transistorfet/z280/software/src/monitor/monitor.c

#include <stdio.h>
#include <stdint.h>
#include <string.h>
#include <stdlib.h>

#include "uart.h"


#define ROM_ADDR	0x000000
#define ROM_SIZE	0x1800

#define RAM_ADDR	0x2000
#define RAM_SIZE	1024

void delay(int count)
{
	while (--count > 0) { __asm__(""); }
}

int readline(char *buffer, short max)
{
	short i = 0;

	while (i < max) {
		buffer[i] = getchar();
		switch (buffer[i]) {
			case 0x08: {
				if (i >= 1) {
					putchar(0x08);
					putchar(' ');
					putchar(0x08);
					i--;
				}
				break;
			}
			case '\n': {
				putchar(buffer[i]);
				buffer[i] = '\0';
				return i;
			}
			default: {
				putchar(buffer[i++]);
				break;
			}
		}
	}
	return i;
}

int parseline(char *input, char **vargs)
{
	short j = 0;

	while (*input == ' ')
		input++;

	vargs[j++] = input;
	while (*input != '\0' && *input != '\n' && *input != '\r') {
		if (*input == ' ') {
			*input = '\0';
			input++;
			while (*input == ' ')
				input++;
			vargs[j++] = input;
		}
		else
 			input++;
	}

	*input = '\0';
	if (*vargs[j - 1] == '\0')
		j -= 1;
	vargs[j] = NULL;

	return j;
}

char hexchar(uint8_t byte)
{
    if (byte < 10)
	return byte + 0x30;
    else
	return byte + 0x37;
}

void dump(const uint8_t *addr, short len)
{
	char buffer[4];

	buffer[2] = ' ';
	buffer[3] = '\0';
	while (len > 0) {
		printf("%x: ", addr);
		for (short i = 0; i < 16 && len > 0; i++, len--) {
			buffer[0] = hexchar((addr[i] >> 4) & 0xF);
			buffer[1] = hexchar(addr[i] & 0x0F);
			fputs(buffer, stdout);
		}
		putchar('\n');
		addr += 16;
	}
	putchar('\n');
}

void command_dump(int argc, char **args)
{
	if (argc <= 1)
		fputs("You need an address\n", stdout);
	else {
		short length = 0x40;

		if (argc >= 3)
			length = strtol(args[2], NULL, 16);
		dump((const uint16_t *) strtol(args[1], NULL, 16), length);
	}
}

void command_poke(int argc, char **args)
{
	if (argc <= 2)
		fputs("You need an address and byte to poke\n", stdout);
	else {
		uint8_t *address = (uint8_t *) strtol(args[1], NULL, 16);
		uint8_t data = (uint8_t) strtol(args[2], NULL, 16);
		*(address) = data;
	}

}

/*
#define SECTOR_SIZE	0x020000

void erase_flash(uint32_t sector)
{
	printf("Erasing flash sector %d", sector);
	*((volatile uint16_t *) (0x555 << 1)) = 0xAAAA;
	putchar('.');
	*((volatile uint16_t *) (0x2AA << 1)) = 0x5555;
	putchar('.');
	*((volatile uint16_t *) (0x555 << 1)) = 0x8080;
	putchar('.');
	*((volatile uint16_t *) (0x555 << 1)) = 0xAAAA;
	putchar('.');
	*((volatile uint16_t *) (0x2AA << 1)) = 0x5555;
	putchar('.');
	*((volatile uint16_t *) sector) = 0x3030;
	putchar('.');
}

void command_eraserom(int argc, char **args)
{
	uint16_t data;
	uint16_t *dest = (uint16_t *) ROM_ADDR;
	uint32_t sector = 0;

	if (argc >= 2) {
		sector = strtol(args[1], NULL, 16);
		if ((sector & (SECTOR_SIZE - 1)) || (sector >= RAM_ADDR)) {
			printf("Invalid sector address to erase (%x)\n", sector);
			return;
		}
		dest = (uint16_t *) sector;
	}

	erase_flash(sector);
	delay(300000);
	data = dest[0];

	fputs("\nVerifying erase\n\n", stdout);
	for (int i = 0; i < ROM_SIZE; i++) {
		data = dest[i];
		if (data != 0xFFFF) {
			printf("Flash not erased at %x (%x)\n", dest + i, data);
			return;
		}
	}

	fputs("Rom erased! Make sure to writerom before resetting\n\n", stdout);
}

void program_flash_data(uint16_t *addr, uint16_t data)
{
	*((volatile uint16_t *) (0x555 << 1)) = 0xAAAA;
	*((volatile uint16_t *) (0x2AA << 1)) = 0x5555;
	*((volatile uint16_t *) (0x555 << 1)) = 0xA0A0;
	*((volatile uint16_t *) addr) = data;
}

void command_writerom(int argc, char **args)
{
	uint16_t data;
	uint16_t errors = 0;

	uint16_t *dest = (uint16_t *) ROM_ADDR;
	uint16_t *source = (uint16_t *) RAM_ADDR;

	if (argc >= 2)
		dest = (uint16_t *) strtol(args[1], NULL, 16);

	for (int i = 0; i < ROM_SIZE; i++) {
		data = dest[i];
		if (data != 0xFFFF) {
			printf("Flash not erased at %x (%x)\n", dest + i, data);
			return;
		}
	}

	for (int i = 0; i < ROM_SIZE; i++) {
		program_flash_data(&dest[i], source[i]);
		delay(200);
		printf("%x ", dest[i]);
	}

	fputs("\nWrite complete\n", stdout);
}

void command_verifyrom(int argc, char **args)
{
	uint16_t data;
	uint16_t errors = 0;

	uint16_t *source = (uint16_t *) RAM_ADDR;
	uint16_t *dest = (uint16_t *) ROM_ADDR;

	if (argc >= 2)
		dest = (uint16_t *) strtol(args[1], NULL, 16);

	for (int i = 0; i < ROM_SIZE; i++) {
		if (dest[i] != source[i]) {
			printf("@%x expected %x but found %x\n", &dest[i], source[i], dest[i]);
			if (++errors > 100) {
				fputs("Bailing out\n", stdout);
				break;
			}
		}
	}

	fputs("\nVerification complete\n", stdout);
}
*/


uint8_t fetch_byte()
{
	char buffer[2];

	for (char i = 0; i < 2; i++) {
		buffer[i] = getchar();
		buffer[i] = buffer[i] <= '9' ? buffer[i] - 0x30 : buffer[i] - 0x37;
	}

	return (buffer[0] << 4) | buffer[1];
}

uint16_t fetch_word()
{
	char buffer[4];

	for (char i = 0; i < 4; i++) {
		buffer[i] = getchar();
		buffer[i] = buffer[i] <= '9' ? buffer[i] - 0x30 : buffer[i] - 0x37;
	}

	return (buffer[0] << 12) | (buffer[1] << 8) | (buffer[2] << 4) | buffer[3];
}

void command_load(int argc, char **args)
{
	int i;
	uint32_t size;
	uint16_t data;
	uint8_t *mem = (uint8_t *) RAM_ADDR;

	size = fetch_word();
	//printf("Expecting %x\n", size);

	if (argc >= 2)
		mem = (uint8_t *) strtol(args[1], NULL, 16);

	for (i = 0; i < size; i++) {
		data = fetch_byte();
		//printf("%x ", data);
		mem[i] = data;
	}

	fputs("Load complete\n", stdout);
}



void command_boot(int argc, char **args)
{
	void (*entry)() = (void (*)()) RAM_ADDR;

	if (argc >= 2)
		entry = (void (*)()) strtol(args[1], NULL, 16);
	//((void (*)()) entry)();
}

void command_serialtest(int argc, char **args)
{
	while (1) {
		int ch = getchar();
		if (ch == 0x1B)
			break;
		putchar(hexchar(ch >> 4));
		putchar(hexchar(ch & 0x0F));
	}
	putchar('\n');
}

void command_ramtest(int argc, char **args)
{
	uint8_t data;
	int errors = 0;

	uint8_t *mem = (uint8_t *) RAM_ADDR;
	for (int i = 0; i < RAM_SIZE; i++) {
		mem[i] = (uint8_t) i;
	}

	for (int i = 0; i < RAM_SIZE; i++) {
		data = (uint8_t) mem[i];
		printf("%x ", data);
		if (data != i)
			errors++;
	}

	printf("\nErrors: %d", errors);
}

/**************************
 * Command Line Execution *
 **************************/

struct command {
	const char *name;
	void (*func)(int, char **);
};

#define add_command(n, f)	{			\
	command_list[num_commands].name = (n);		\
	command_list[num_commands++].func = (f);	\
}

int load_commands(struct command *command_list)
{
	int num_commands = 0;

	//add_command("info", command_info);
	add_command("load", command_load);
	add_command("boot", command_boot);
	add_command("dump", command_dump);
	add_command("poke", command_poke);
	//add_command("dumpram", command_dumpram);
	//add_command("eraserom", command_eraserom);
	//add_command("writerom", command_writerom);
	//add_command("verifyrom", command_verifyrom);

	add_command("serialtest", command_serialtest);
	add_command("ramtest", command_ramtest);

	return num_commands;
}

#define BUF_SIZE	100
#define ARG_SIZE	10

void serial_read_loop()
{
	int i;
	short argc;
	char buffer[BUF_SIZE];
	char *args[ARG_SIZE];

	struct command command_list[20];
	int num_commands = load_commands(command_list);

	while (1) {
		fputs("> ", stdout);
		readline(buffer, BUF_SIZE);
		argc = parseline(buffer, args);

		if (!strcmp(args[0], "test")) {
			fputs("this is only a test\n", stdout);
		}
		else if (!strcmp(args[0], "help")) {
			for (int i = 0; i < num_commands; i++) {
				fputs(command_list[i].name, stdout);
				putchar('\n');
			}
		}
		else {
			for (i = 0; i < num_commands; i++) {
				if (!strcmp(args[0], command_list[i].name)) {
					command_list[i].func(argc, args);
					break;
				}
			}

			if (i >= num_commands && args[0][0] != '\0') {
				fputs("Unknown command\n", stdout);
			}
		}
	}
}



void main()
{
	init_uart();

	puts("Welcome to the Z280!\n\n");

	serial_read_loop();

	return;
}
 
